YeetTheAnson/ParametricSpeaker/04_LTspice/pulse.asc

C1: cap; 0.1µ
C2: cap; 0.1µ
C3: cap; 3.3n
L1: ind; 4.7m
R1: res; 1k
R2: res; 100k
R3: res; 100k
V1: voltage; SINE(0 8 40.3k)
V2: voltage; PULSE(0 1 0 0.1n 0.1n 12.4u 24.8u)
Named nets: 0, SIG, SIG2
.tran 10m
