YeetTheAnson/ParametricSpeaker/04_LTspice/amp.asc

B1: bv; V= 8+V(Vin1) +V(Vin1)*V(Vin2)
C1: cap; 1µ
C2: polcap; 22µ; V=35 Irms=413m Rser=0.22 Lser=0
C3: cap; 0.01µ
C4: polcap; 22µ; V=35 Irms=413m Rser=0.22 Lser=0
C5: cap; 2000p
L1: ind; 6.6m
R1: res; 100k
R2: res; 220k
R3: res; 1k
R4: res; 10k
R5: res; 10k
R6: res; 5
R8: res; 1k
R9: res; 10k
U1: OP284
U2: LT1210
V1: voltage; SINE(0 0.5 40k)
V2: voltage; SINE(0 1 400)
V3: voltage; 12
V4: voltage; 12
Named nets: 0, Vin1, Vin2, SIG, Vcc, Vee, SIG_AC
.tran 40ms
.options plotwinsize=0
.include LM1875.lib
