YeetTheAnson/ParametricSpeaker/04_LTspice/LC-resonance.asc

C1: cap; 130p
C2: cap; 2100p
C3: cap; 130p
C4: cap; 2100p
C5: cap; 2400p
C6: cap; 2400p
C7: cap; 2400p
C8: cap; 2400p
C9: cap; 2400p
C10: cap; 2400p
L1: ind2; 5m; Rser=2m
L2: ind; 120m
L3: ind2; 430m
L4: ind; 120m
L5: ind; 6.6m
R1: res; 800
R2: res; 800
R3: res; 1
R4: res; 1
R5: res; 1
R6: res; 1
R7: res; 1
R8: res; 1
V1: voltage; SINE(0 8 40.3k)
Named nets: 0, SIG
.tran 10m
K1 L1 L3 1
.step param L list 0.1n 0.1u 0.1m
